porbital/GNC_Hapsis/10_30_2025_test/log_20000101_000006.csv

Time | Angular Position | R Solenoid | L Solenoid | Angular Vel X | Angular Vel Y | Angular Vel Z | PID Error | P | D
4.112 | 356.25 | 0 | 0 | -0.0239983 | -0.434151 | 0.199622 | 2.51038 | 3.75 | 0.911965
0.0509987 | 354.875 | 1 | 0 | -0.01309 | -0.441787 | 0.187623 | 15.0027 | 5.125 | 26.9615
0.0510006 | 353.438 | 1 | 0 | -0.00654499 | -0.440696 | 0.165806 | 16.3587 | 6.5625 | 28.1859
0.052 | 352.188 | 1 | 0 | 0.00436333 | -0.423243 | 0.150535 | 15.1923 | 7.8125 | 24.0384
0.052 | 351.063 | 1 | 0 | 0.00981748 | -0.362156 | 0.133081 | 14.7406 | 8.9375 | 21.6346
0.052 | 349.813 | 1 | 0 | 0.00763582 | -0.343612 | 0.110174 | 16.5223 | 10.1875 | 24.0384
0.0559998 | 349.0 | 1 | 0 | 0.00545416 | -0.282525 | 0.0981748 | 12.689 | 11.0 | 14.509
0.0510006 | 348.375 | 1 | 0 | 0.00327249 | -0.21053 | 0.0796307 | 12.0246 | 11.625 | 12.2548
0.0510006 | 347.938 | 1 | 0 | -0.00436333 | -0.11781 | 0.0545416 | 10.6152 | 12.0625 | 8.57833
0.0509987 | 347.625 | 1 | 0 | -0.01309 | -0.077449 | 0.0381791 | 9.68742 | 12.375 | 6.12761
0.0489998 | 347.438 | 1 | 0 | -0.0119991 | -0.0414516 | 0.0109083 | 8.75694 | 12.5625 | 3.82655
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
