porbital/GNC_Hapsis/10_30_2025_test/log_20000101_000012.csv

Time | Angular Position | R Solenoid | L Solenoid | Angular Vel X | Angular Vel Y | Angular Vel Z | PID Error | P | D
3.606 | 359.688 | 0 | 0 | -0.00436333 | -0.0414516 | 0.0119991 | 0.213997 | 0.3125 | 0.086661
0.0669975 | 359.563 | 1 | 0 | -0.00436333 | -0.0338158 | 0.00763582 | 1.08458 | 0.4375 | 1.86574
0.0670013 | 359.5 | 1 | 0 | 0.0 | -0.0272708 | 0.00654499 | 0.699767 | 0.5 | 0.932817
0.0670013 | 359.438 | 1 | 0 | 0.00436333 | -0.0229075 | 0.00218166 | 0.734767 | 0.5625 | 0.932817
0.0659981 | 359.375 | 1 | 0 | 0.0 | -0.019635 | -0.00109083 | 0.776149 | 0.625 | 0.946997
0.0680008 | 359.313 | 1 | 0 | 0.0 | -0.0207258 | -0.00218166 | 0.798598 | 0.6875 | 0.919107
0.0719986 | 359.25 | 1 | 0 | 0.00218166 | -0.0163625 | -0.00545416 | 0.810633 | 0.75 | 0.868073
0.0660019 | 359.188 | 1 | 0 | -0.00109083 | -0.0174533 | -0.0119991 | 0.881124 | 0.8125 | 0.946943
0.0670013 | 359.188 | 1 | 0 | -0.00109083 | -0.00763582 | -0.0109083 | 0.455 | 0.8125 | 0.0
0.0669975 | 359.188 | 1 | 0 | -0.00436333 | -0.00872665 | -0.0141808 | 0.455 | 0.8125 | 0.0
0.0660019 | 359.25 | 1 | 0 | -0.00327249 | 0.00872665 | -0.0119991 | -0.00612414 | 0.75 | -0.946943
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
