porbital/GNC_Hapsis/STAG/flight_controller_v3/src/Logging.h

#ifndef LOGGING_H
#define LOGGING_H

#include <Arduino.h>
#include "Config.h"
#include <SPI.h>
#include <SdFat.h>
#include "MissionState.h"

#define CS_PIN 10
#define SCK_PIN 13
#define MISO_PIN 12
#define MOSI_PIN 11

// Initialize SD card and file for logging
void initLogging();

// Log data to SD card
void logData(
    unsigned long timestamp,
    float temperature, float pressure, float altitude,
    float roll, float pitch, float heading, float vertical_accel,
    float vertical_vel,
    bool leftThruster, bool rightThruster,
    MissionState state
);

// Log event to SD Card
void logEvent(const String &eventDescription);

#endif
